ysoldak/HeadTracker/case/xiao-micro-case-wired.jpg

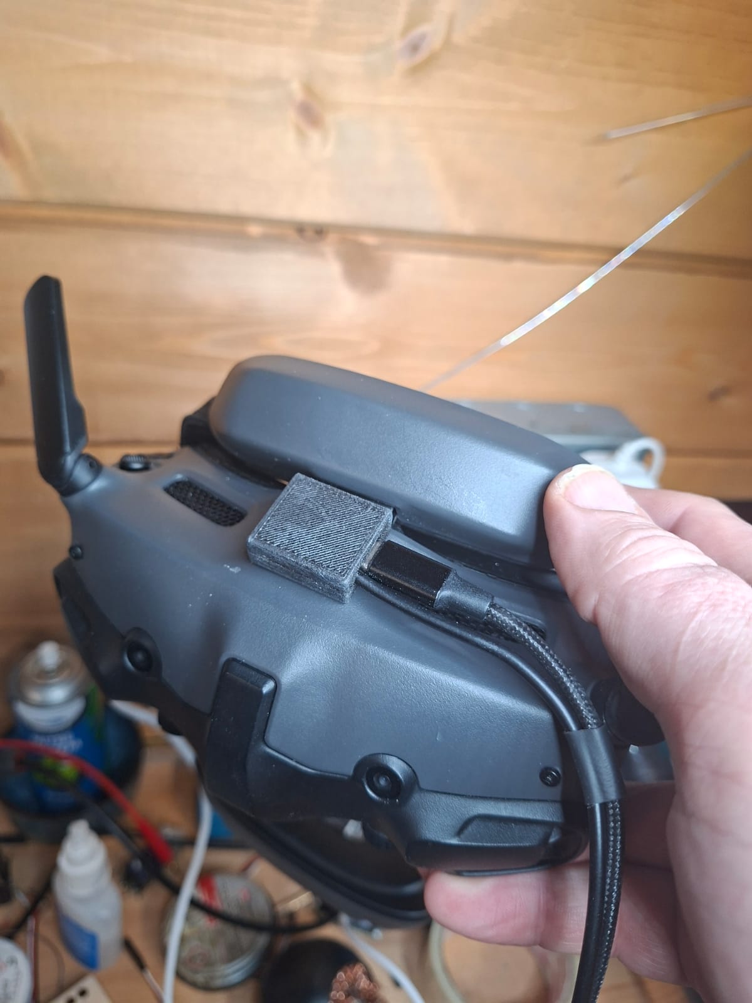
case/xiao-micro-case-wired.jpg
