ysoldak/HeadTracker/case/XiaoBle1Closed.jpg

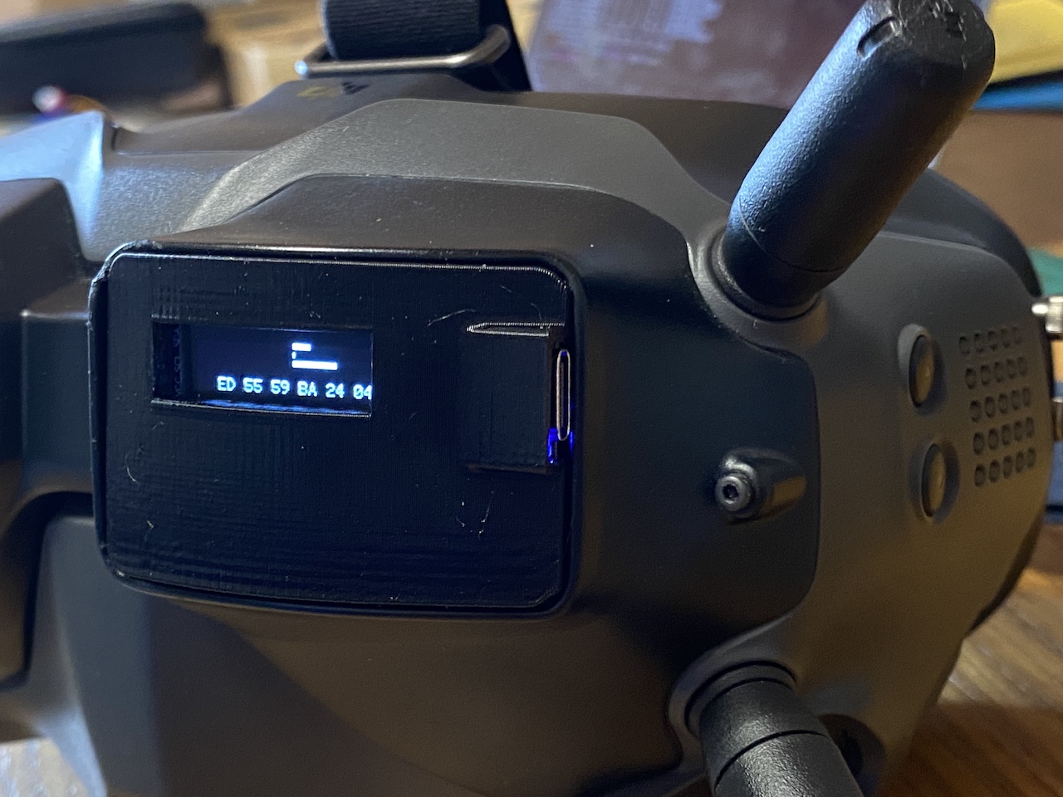
case/XiaoBle1Closed.jpg
