ysoldak/HeadTracker/case/XiaoBle1Open.jpg

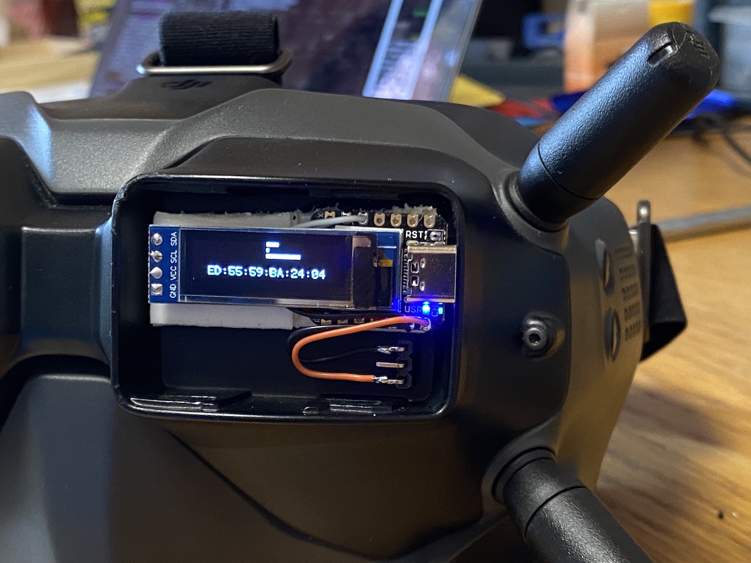
case/XiaoBle1Open.jpg
