ysoldak/HeadTracker/case/GogglesX Xiao Ble Lock.stl

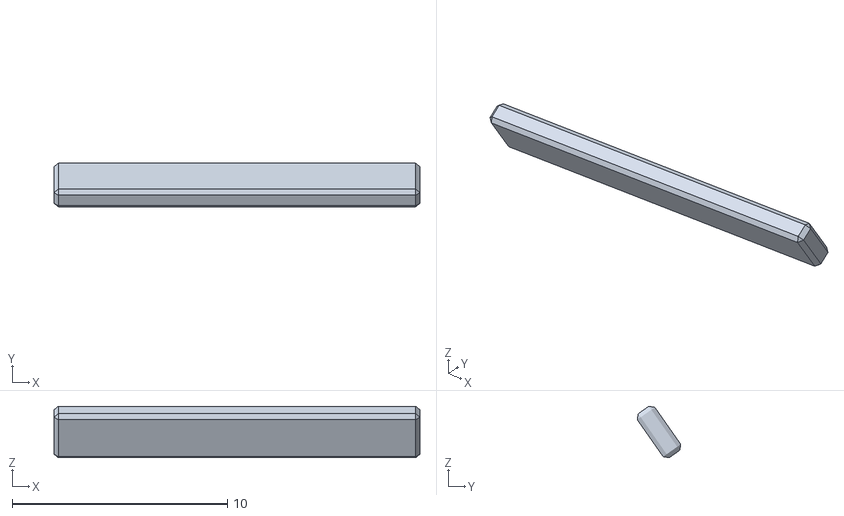
[picture p36: CAD file, 2024-03-11]
case/GogglesX Xiao Ble Lock.stl
17.0 x 2.02 x 2.39
