ysoldak/HeadTracker/case/XiaoBle2.3mf

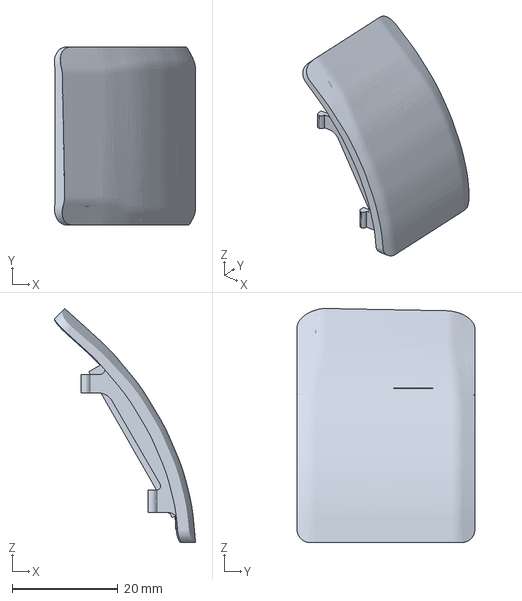
[picture p37: CAD file, 2022-08-15]
case/XiaoBle2.3mf
26.7 x 33.6 x 44.2 mm
