ysoldak/HeadTracker/case/Nano33Ble-Clip.stl

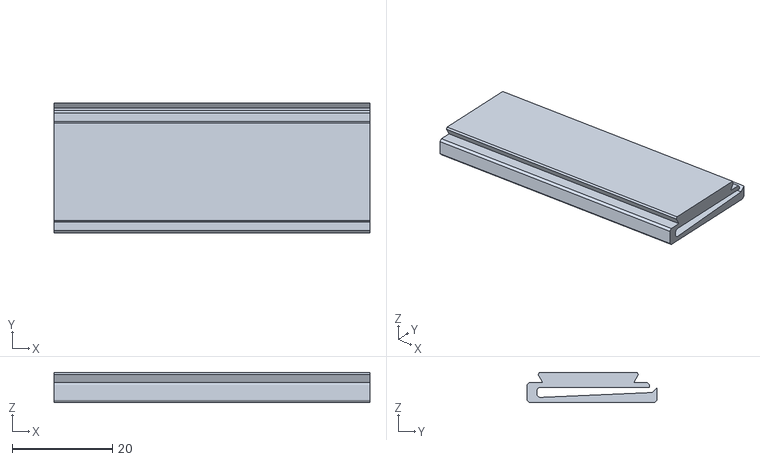
[picture p38: CAD file, 2021-02-01]
case/Nano33Ble-Clip.stl
63.0 x 26.0 x 6.00
